antmicro/sdi-mipi-bridge-hw/assets/previews/layer1.png

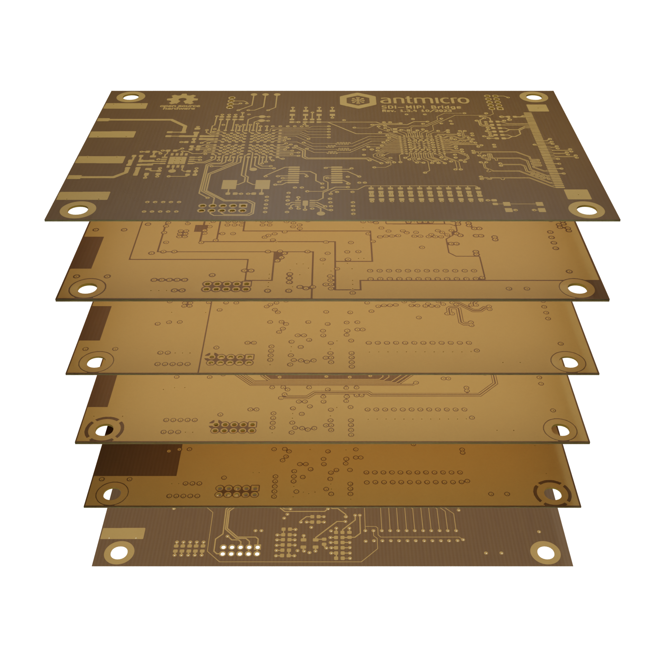
assets/previews/layer1.png
