antmicro/sdi-mipi-bridge-hw/assets/previews/layer2_thumbnail.png

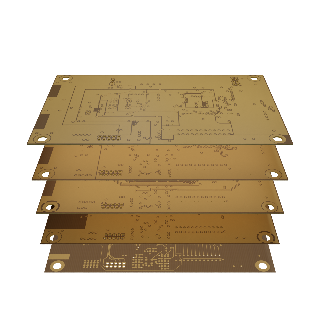
assets/previews/layer2_thumbnail.png
