antmicro/sdi-mipi-bridge-hw/assets/previews/layer3.png

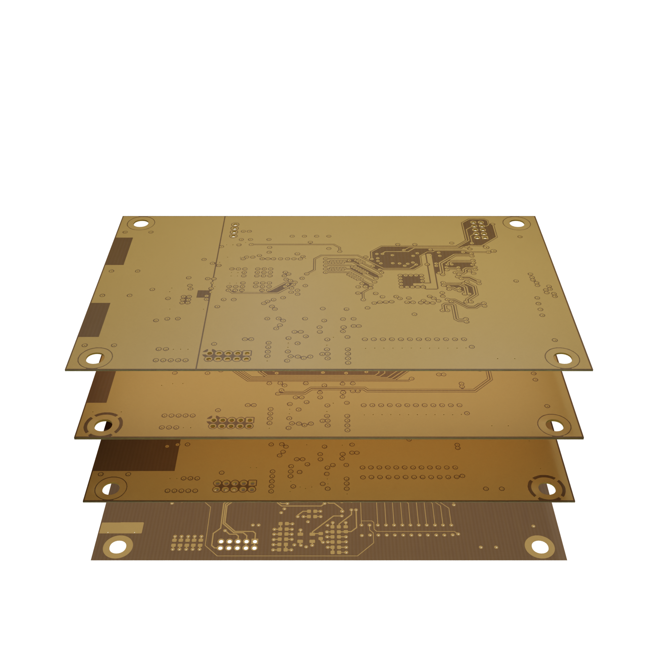
assets/previews/layer3.png
