antmicro/sdi-mipi-bridge-hw/assets/previews/layer4.png

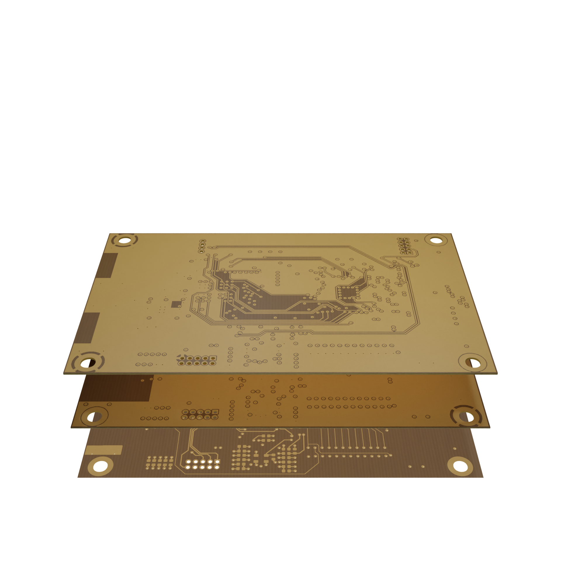
assets/previews/layer4.png
