antmicro/sdi-mipi-bridge-hw/assets/previews/layer5.png

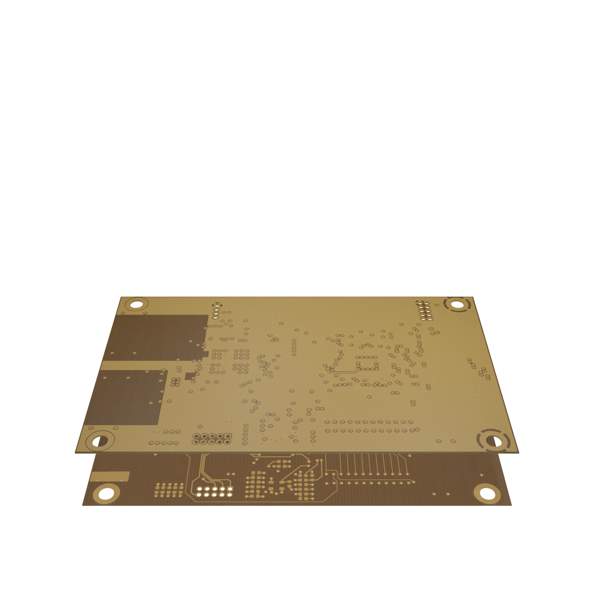
assets/previews/layer5.png
