antmicro/sdi-mipi-bridge-hw/assets/previews/leftB.png

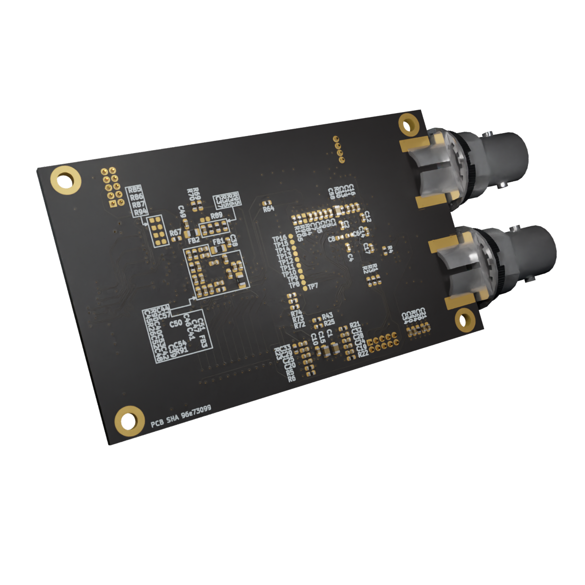
assets/previews/leftB.png
