antmicro/sdi-mipi-bridge-hw/assets/previews/leftT.png

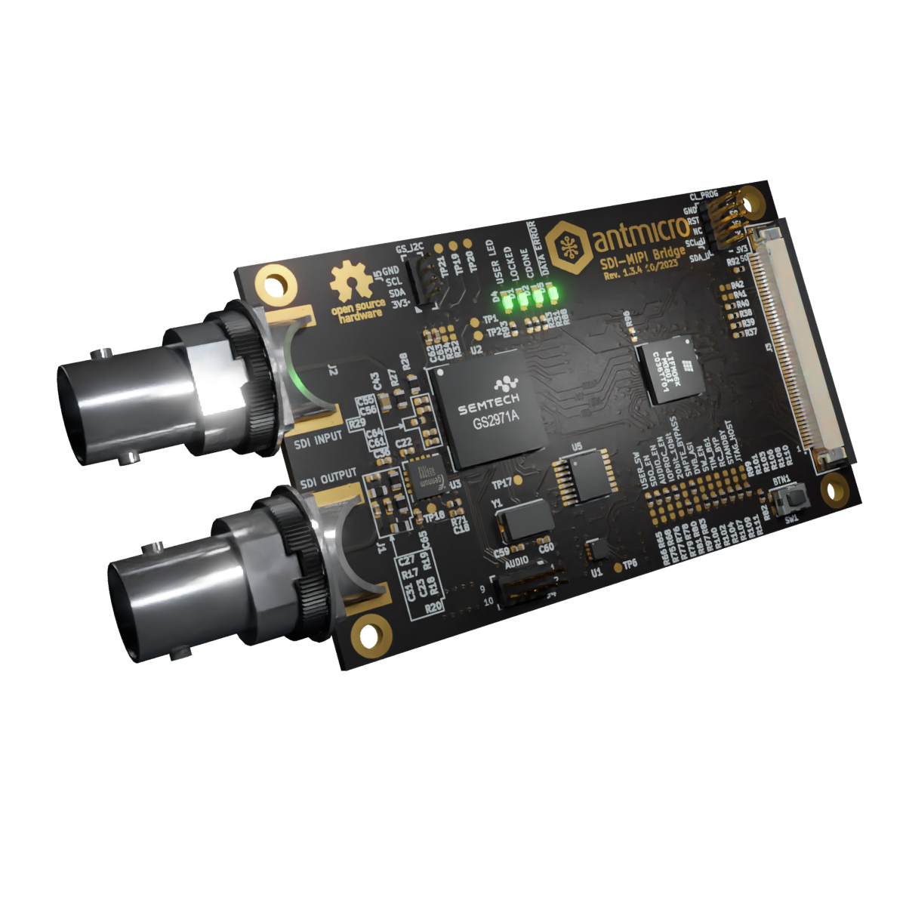
assets/previews/leftT.png
