antmicro/sdi-mipi-bridge-hw/assets/previews/orthoB.png

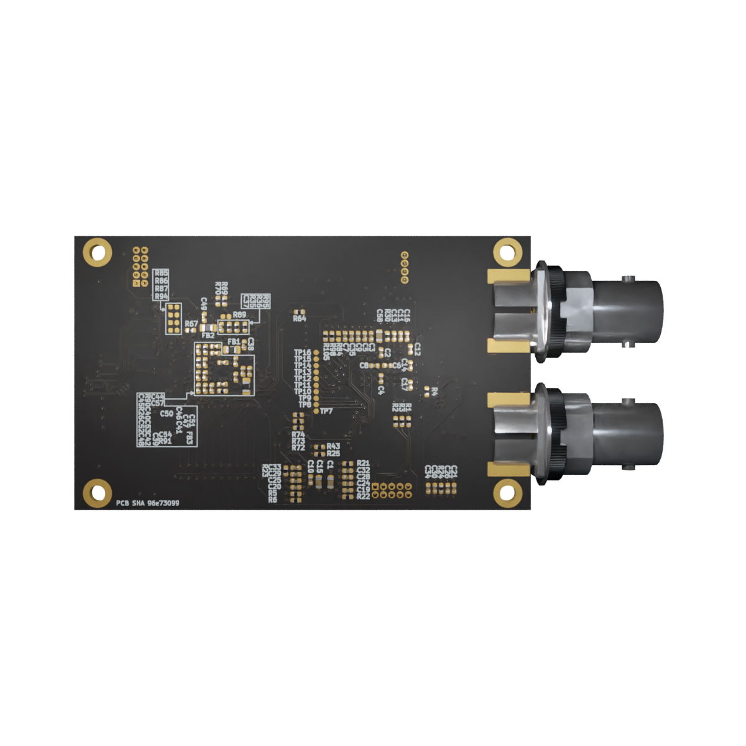
assets/previews/orthoB.png
