antmicro/sdi-mipi-bridge-hw/assets/previews/orthoT.png

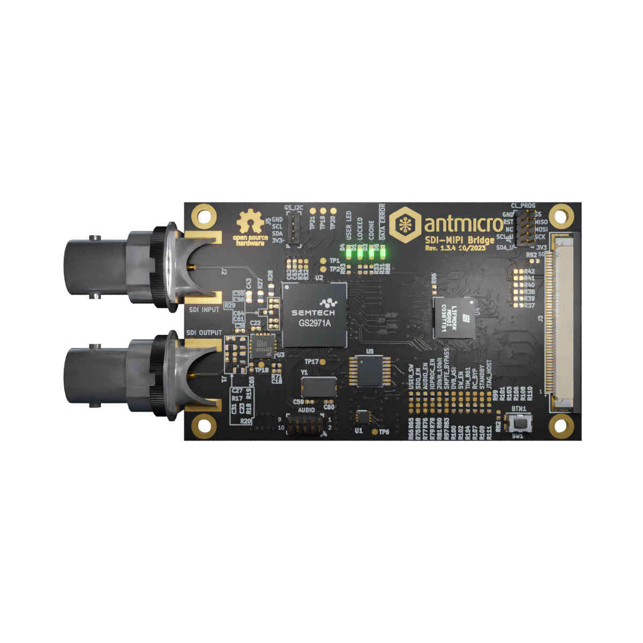
assets/previews/orthoT.png
