antmicro/sdi-mipi-bridge-hw/assets/previews/photoB.png

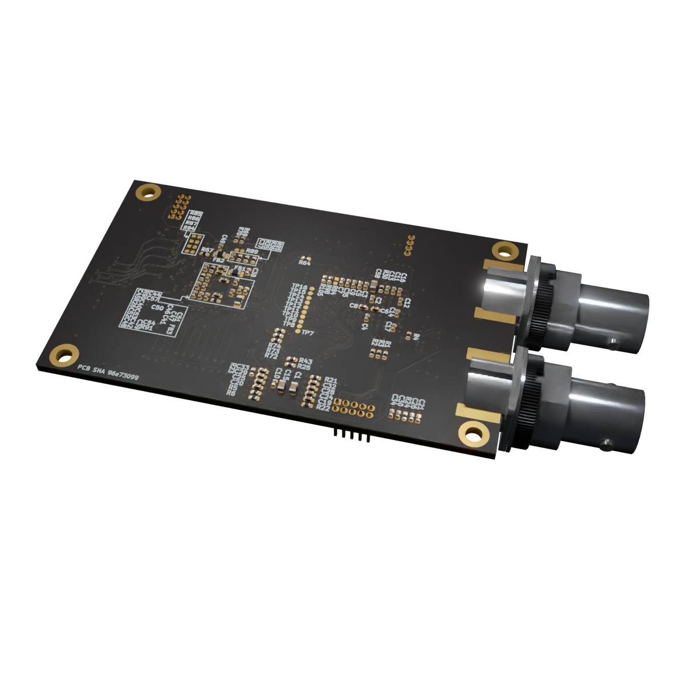
assets/previews/photoB.png
