antmicro/sdi-mipi-bridge-hw/assets/previews/photoT.png

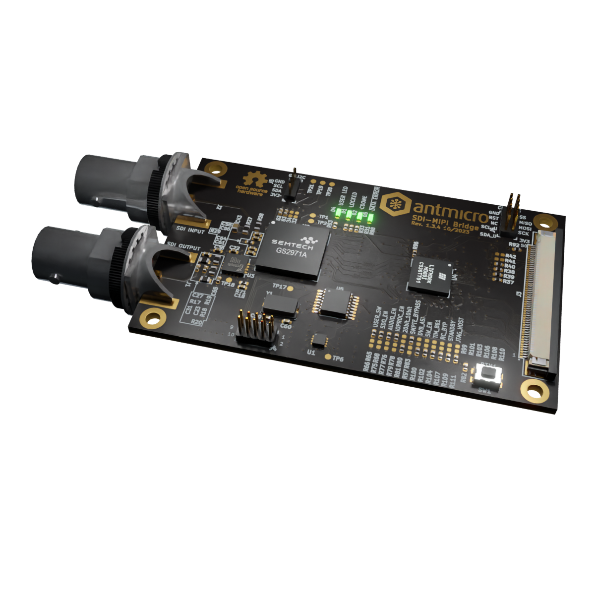
assets/previews/photoT.png
