antmicro/sdi-mipi-bridge-hw/assets/previews/rightB.png

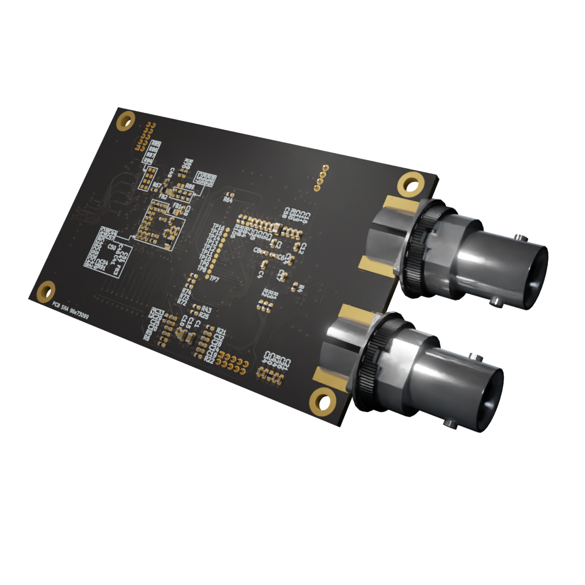
assets/previews/rightB.png
