antmicro/sdi-mipi-bridge-hw/assets/previews/rightT.png

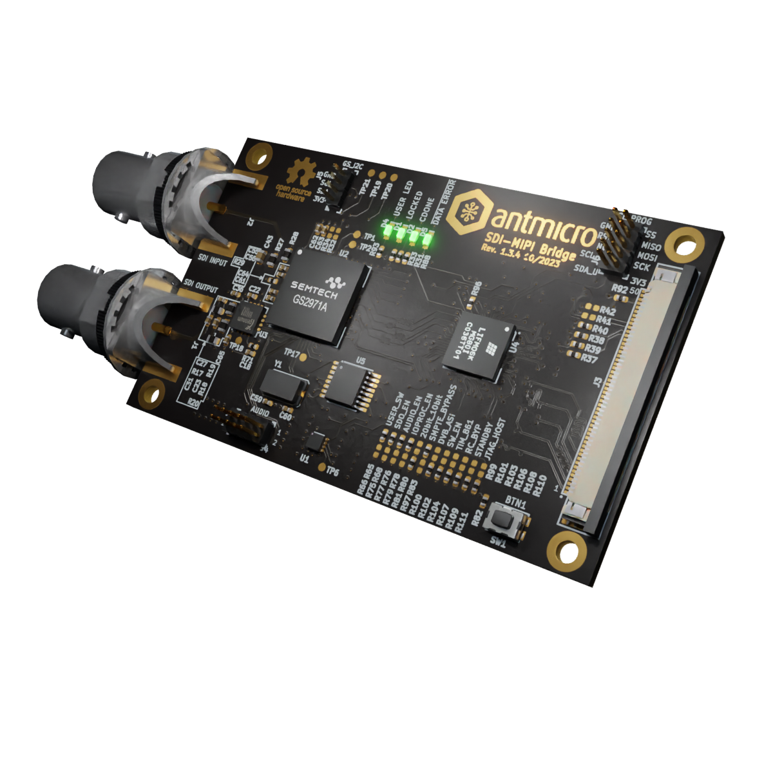
assets/previews/rightT.png
