antmicro/sdi-mipi-bridge-hw/img/SDI_dimensions.png

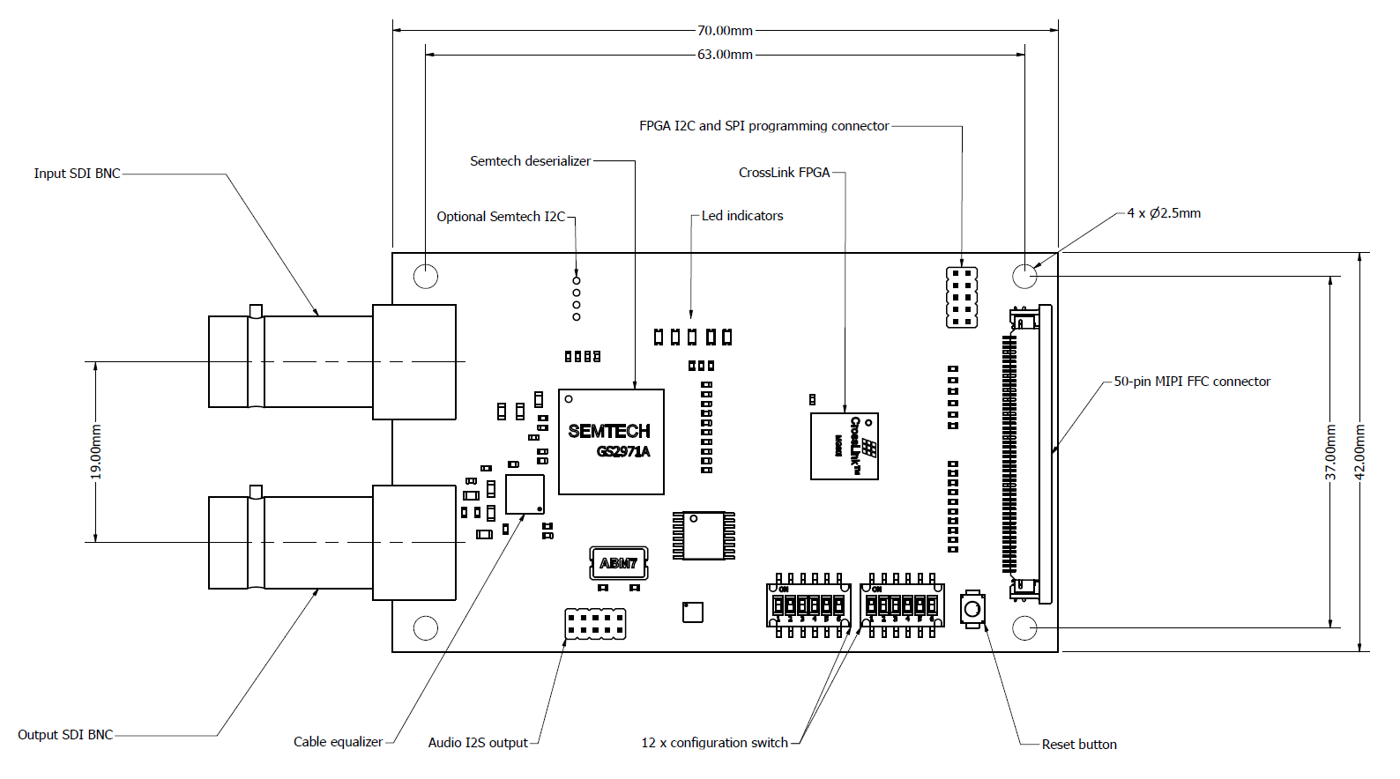
img/SDI_dimensions.png
